TilenTinta/Resin_printed_PCB_stencil/Images/PXL_20250601_203703660.jpg

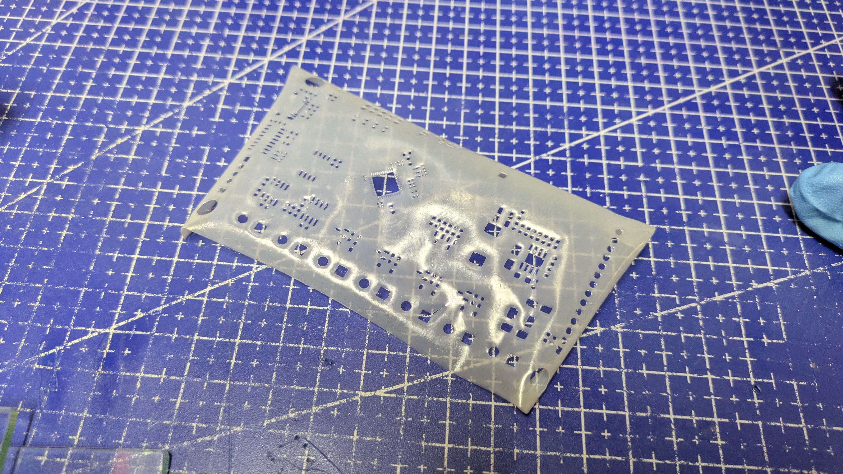
Images/PXL_20250601_203703660.jpg
