TilenTinta/Resin_printed_PCB_stencil/Images/PXL_20250601_203725748.jpg

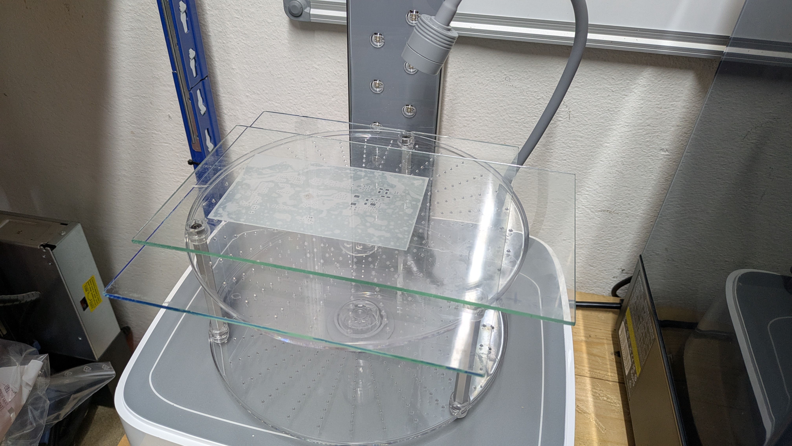
Images/PXL_20250601_203725748.jpg
