TilenTinta/Resin_printed_PCB_stencil/Images/PXL_20250601_204256586.jpg

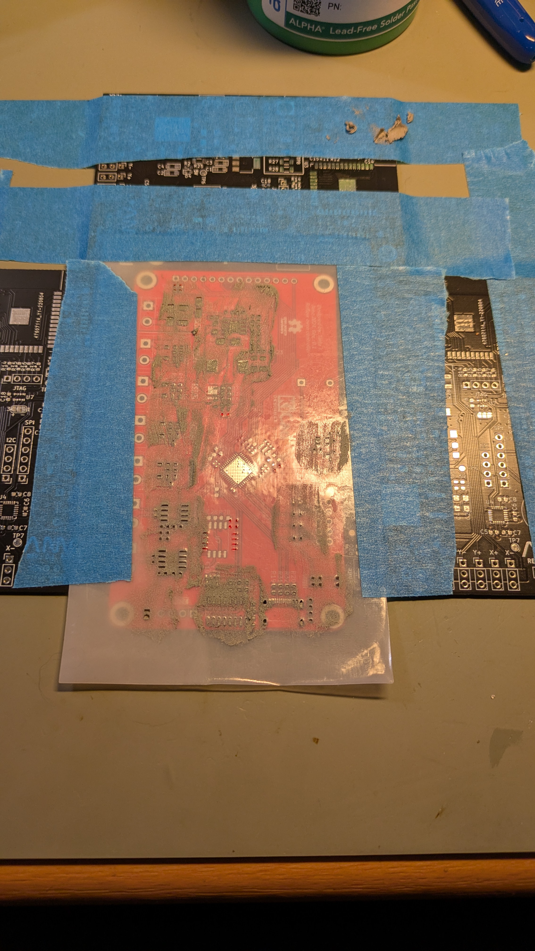
Images/PXL_20250601_204256586.jpg
