TilenTinta/Resin_printed_PCB_stencil/Images/PXL_20250601_204409662.jpg

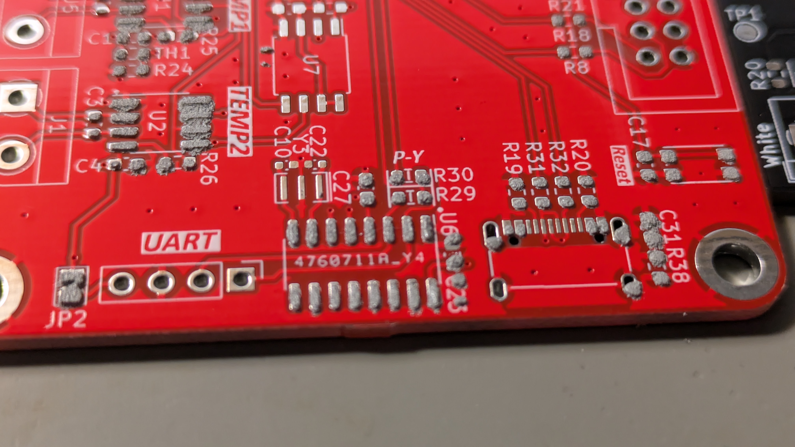
Images/PXL_20250601_204409662.jpg
