TilenTinta/Resin_printed_PCB_stencil/Images/PXL_20250601_204617746.jpg

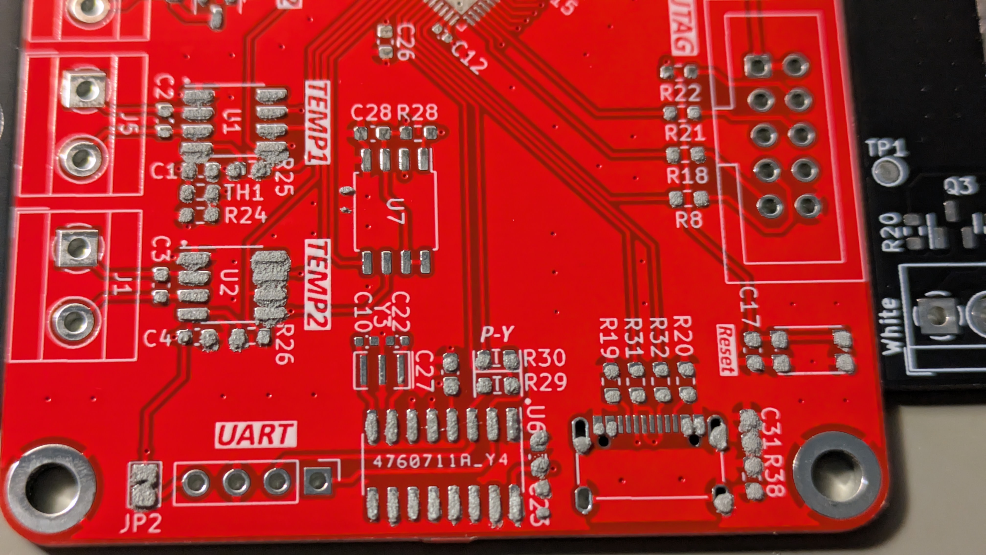
Images/PXL_20250601_204617746.jpg
