TilenTinta/Resin_printed_PCB_stencil/Images/PXL_20250601_205113436.jpg

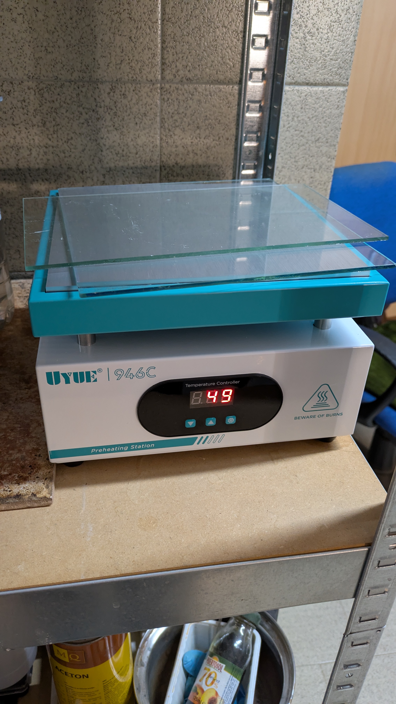
Images/PXL_20250601_205113436.jpg
